ElconicsSuraj/LoRaWAN-Smart-Energy-Meter/code/Smart-energy-meter/Energymeter-chirpsatck-main/STM32WL-standalone/Core/gpio.c

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

/* Includes ------------------------------------------------------------------*/
#include "gpio.h"

/*----------------------------------------------------------------------------*/
/* Configure GPIO                                                             */
/*----------------------------------------------------------------------------*/
/** Configure pins as
        * Analog
        * Input
        * Output
        * EVENT_OUT
        * EXTI
*/
void MX_GPIO_Init(void)
{

	 GPIO_InitTypeDef GPIO_InitStruct = {0};

	  /* GPIO Ports Clock Enable */
	  __HAL_RCC_GPIOB_CLK_ENABLE();
	  __HAL_RCC_GPIOC_CLK_ENABLE();
	  __HAL_RCC_GPIOA_CLK_ENABLE();

	  /*Configure GPIO pin Output Level */

	  HAL_GPIO_WritePin(GPIOB, CTRL1_PIN_Pin, GPIO_PIN_RESET);
	  GPIO_InitStruct.Pin = CTRL1_PIN_Pin;
	  GPIO_InitStruct.Mode = GPIO_MODE_OUTPUT_PP;
	  GPIO_InitStruct.Pull = GPIO_NOPULL;
	  GPIO_InitStruct.Speed = GPIO_SPEED_FREQ_HIGH;
	  HAL_GPIO_Init(GPIOB, &GPIO_InitStruct);


	  HAL_GPIO_WritePin(GPIOA, RED_LED_Pin|BLUE_LED_Pin|GREEN_LED_Pin|RF_Supply_SW_Pin, GPIO_PIN_RESET);
	  GPIO_InitStruct.Pin = RED_LED_Pin|BLUE_LED_Pin|GREEN_LED_Pin|RF_Supply_SW_Pin;
	  GPIO_InitStruct.Mode = GPIO_MODE_OUTPUT_PP;
	  GPIO_InitStruct.Pull = GPIO_NOPULL;
	  GPIO_InitStruct.Speed = GPIO_SPEED_FREQ_HIGH;
	  HAL_GPIO_Init(GPIOA, &GPIO_InitStruct);

	  GPIO_InitStruct.Pin = USER_SW_Pin;
	  GPIO_InitStruct.Mode = GPIO_MODE_IT_FALLING;
	  GPIO_InitStruct.Pull = GPIO_NOPULL;
	  HAL_GPIO_Init(USER_SW_GPIO_Port, &GPIO_InitStruct);

	  HAL_NVIC_SetPriority(EXTI15_10_IRQn, 0, 0);
	  HAL_NVIC_EnableIRQ(EXTI15_10_IRQn);

	  HAL_NVIC_SetPriority(EXTI0_IRQn, 0, 0);
	  HAL_NVIC_EnableIRQ(EXTI0_IRQn);

	  HAL_NVIC_SetPriority(EXTI1_IRQn, 0, 0);
	  HAL_NVIC_EnableIRQ(EXTI1_IRQn);

	  HAL_NVIC_SetPriority(EXTI9_5_IRQn, 0, 0);
	  HAL_NVIC_EnableIRQ(EXTI9_5_IRQn);

	  GPIO_InitStruct.Pin = VIBRATION_SENSOR_Pin;
	  GPIO_InitStruct.Mode = GPIO_MODE_IT_FALLING;
	  GPIO_InitStruct.Pull = GPIO_PULLUP;
	  HAL_GPIO_Init(VIBRATION_SENSOR_GPIO_Port, &GPIO_InitStruct);

	  HAL_NVIC_SetPriority(VIBRATION_SENSOR_EXTI_IRQn, 0, 0);
	  HAL_NVIC_EnableIRQ(VIBRATION_SENSOR_EXTI_IRQn);

}

/* USER CODE BEGIN 2 */


void configure_gpio_pins_as_input(void)
{
	GPIO_InitTypeDef GPIO_InitStruct = {0};

	GPIO_InitStruct.Pin = RED_LED_Pin;
	GPIO_InitStruct.Mode = GPIO_MODE_INPUT;
	GPIO_InitStruct.Pull = GPIO_PULLDOWN;
	HAL_GPIO_Init(RED_LED_GPIO_Port, &GPIO_InitStruct);

	GPIO_InitStruct.Pin = BLUE_LED_Pin;
	GPIO_InitStruct.Mode = GPIO_MODE_INPUT;
	GPIO_InitStruct.Pull = GPIO_PULLDOWN;
	HAL_GPIO_Init(BLUE_LED_GPIO_Port, &GPIO_InitStruct);

	GPIO_InitStruct.Pin = GREEN_LED_Pin;
	GPIO_InitStruct.Mode = GPIO_MODE_INPUT;
	GPIO_InitStruct.Pull = GPIO_PULLDOWN;
	HAL_GPIO_Init(GREEN_LED_GPIO_Port, &GPIO_InitStruct);


	GPIO_InitStruct.Pin = RF_Supply_SW_Pin;
	GPIO_InitStruct.Mode = GPIO_MODE_INPUT;
	GPIO_InitStruct.Pull = GPIO_PULLDOWN;
	HAL_GPIO_Init(GPIOA, &GPIO_InitStruct);


	GPIO_InitStruct.Pin = CTRL1_PIN_Pin;
	GPIO_InitStruct.Mode = GPIO_MODE_INPUT;
	GPIO_InitStruct.Pull = GPIO_PULLDOWN;
	HAL_GPIO_Init(GPIOB, &GPIO_InitStruct);
}


void turn_radio_switch(rf_switch_t state)
{
	if (state == RF_SWITCH_ON)
	{
		HAL_GPIO_WritePin(RF_Supply_SW_GPIO_Port, RF_Supply_SW_Pin, GPIO_PIN_SET);
	}
	else if (state == RF_SWITCH_OFF)
	{
		HAL_GPIO_WritePin(RF_Supply_SW_GPIO_Port, RF_Supply_SW_Pin, GPIO_PIN_RESET);
	}
	HAL_Delay(10);
}


void turn_on_led(led_t led)
{
	if (RED == led)
	{
		HAL_GPIO_WritePin(RED_LED_GPIO_Port, RED_LED_Pin, GPIO_PIN_SET);
	}
	else if (BLUE == led)
	{
		HAL_GPIO_WritePin(BLUE_LED_GPIO_Port, BLUE_LED_Pin, GPIO_PIN_SET);
	}
	else if (GREEN  == led)
	{
		HAL_GPIO_WritePin(GREEN_LED_GPIO_Port, GREEN_LED_Pin, GPIO_PIN_SET);
	}
}


void turn_off_led(led_t led)
{
	if (RED == led)
	{
		HAL_GPIO_WritePin(RED_LED_GPIO_Port, RED_LED_Pin, GPIO_PIN_RESET);
	}
	else if (BLUE == led)
	{
		HAL_GPIO_WritePin(BLUE_LED_GPIO_Port, BLUE_LED_Pin, GPIO_PIN_RESET);
	}
	else if (GREEN  == led)
	{
		HAL_GPIO_WritePin(GREEN_LED_GPIO_Port, GREEN_LED_Pin, GPIO_PIN_RESET);
	}
}

void toggle_led(led_t led)
{
	if (RED == led)
	{
		HAL_GPIO_TogglePin(RED_LED_GPIO_Port, RED_LED_Pin);
	}
	else if (BLUE == led)
	{
		HAL_GPIO_TogglePin(BLUE_LED_GPIO_Port, BLUE_LED_Pin);
	}
	else if (GREEN  == led)
	{
		HAL_GPIO_TogglePin(GREEN_LED_GPIO_Port, GREEN_LED_Pin);
	}
}

/* USER CODE END 2 */
