ElconicsSuraj/LoRaWAN-Smart-Energy-Meter/code/Smart-energy-meter/Energymeter-chirpsatck-main/STM32WL-standalone/Core/usart_if.c

#include "usart_if.h"

extern DMA_HandleTypeDef hdma_usart1_tx;
extern UART_HandleTypeDef huart1;

uint8_t charRx;


const UTIL_ADV_TRACE_Driver_s UTIL_TraceDriver =
{
  vcom_Init,
  vcom_DeInit,
  vcom_ReceiveInit,
  vcom_Trace_DMA,
};


static void (*TxCpltCallback)(void *);
/**
  * @brief  RX complete callback
  * @param  rxChar ptr of chars buffer sent by user
  * @param  size buffer size
  * @param  error errorcode
  * @return none
  */
static void (*RxCpltCallback)(uint8_t *rxChar, uint16_t size, uint8_t error);


UTIL_ADV_TRACE_Status_t vcom_Init(void (*cb)(void *))
{
  TxCpltCallback = cb;
  MX_DMA_Init();
  MX_USART1_UART_Init();
  LL_EXTI_EnableIT_0_31(LL_EXTI_LINE_27);
  return UTIL_ADV_TRACE_OK;
}

UTIL_ADV_TRACE_Status_t vcom_DeInit(void)
{

  /* ##-1- Reset peripherals ################################################## */
  __HAL_RCC_USART1_FORCE_RESET();
  __HAL_RCC_USART1_RELEASE_RESET();

  /* ##-2- MspDeInit ################################################## */
  HAL_UART_MspDeInit(&huart1);

  /* ##-3- Disable the NVIC for DMA ########################################### */
  /* USER CODE BEGIN 1 */
  HAL_NVIC_DisableIRQ(DMA1_Channel5_IRQn);

  return UTIL_ADV_TRACE_OK;
}

void vcom_Trace(uint8_t *p_data, uint16_t size)
{
  HAL_UART_Transmit(&huart1, p_data, size, 1000);
}

UTIL_ADV_TRACE_Status_t vcom_Trace_DMA(uint8_t *p_data, uint16_t size)
{
  HAL_UART_Transmit_DMA(&huart1, p_data, size);
  return UTIL_ADV_TRACE_OK;

}

UTIL_ADV_TRACE_Status_t vcom_ReceiveInit(void (*RxCb)(uint8_t *rxChar, uint16_t size, uint8_t error))
{

  UART_WakeUpTypeDef WakeUpSelection;

  /*record call back*/
  RxCpltCallback = RxCb;

  /*Set wakeUp event on start bit*/
  WakeUpSelection.WakeUpEvent = UART_WAKEUP_ON_STARTBIT;

  HAL_UARTEx_StopModeWakeUpSourceConfig(&huart1, WakeUpSelection);

  /* Make sure that no UART transfer is on-going */
  while (__HAL_UART_GET_FLAG(&huart1, USART_ISR_BUSY) == SET);

  /* Make sure that UART is ready to receive)   */
  while (__HAL_UART_GET_FLAG(&huart1, USART_ISR_REACK) == RESET);

  /* Enable USART interrupt */
  __HAL_UART_ENABLE_IT(&huart1, UART_IT_WUF);

  /*Enable wakeup from stop mode*/
  HAL_UARTEx_EnableStopMode(&huart1);

  /*Start LPUART receive on IT*/
  HAL_UART_Receive_IT(&huart1, &charRx, 1);

  return UTIL_ADV_TRACE_OK;

}

void vcom_Resume(void)
{

  /*to re-enable lost UART settings*/
  if (HAL_UART_Init(&huart1) != HAL_OK)
  {
    Error_Handler();
  }

  /*to re-enable lost DMA settings*/
  if (HAL_DMA_Init(&hdma_usart1_tx) != HAL_OK)
  {
    Error_Handler();
  }

}

void HAL_UART_TxCpltCallback(UART_HandleTypeDef *huart2)
{

  /* buffer transmission complete*/
  TxCpltCallback(NULL);

}

void HAL_UART_RxCpltCallback(UART_HandleTypeDef *huart2)
{
  if ((NULL != RxCpltCallback) && (HAL_UART_ERROR_NONE == huart2->ErrorCode))
  {
    RxCpltCallback(&charRx, 1, 0);
  }
  HAL_UART_Receive_IT(huart2, &charRx, 1);
}
