ElconicsSuraj/LoRaWAN-Smart-Energy-Meter/code/Smart-energy-meter/Energymeter-chirpsatck-main/STM32WL-standalone/Drivers/Inc/usart.h

#ifndef __USART_H__
#define __USART_H__

#ifdef __cplusplus
extern "C" {
#endif

/* Includes ------------------------------------------------------------------*/
#include "main.h"


extern UART_HandleTypeDef huart1;
extern UART_HandleTypeDef huart2;
extern UART_HandleTypeDef hlpuart1;

void MX_USART1_UART_Init(void);
void MX_USART2_UART_Init(void);
void MX_LPUART1_UART_Init(void);



#ifdef __cplusplus
}
#endif

#endif
